arlenko/gem-solder/firmware/source/Core/BSP/Gem/Pins.h

/*
 * Pins.h
 *
 *  Created on: 29 May 2020
 *      Author: Ralim
 */

#ifndef BSP_MINIWARE_PINS_H_
#define BSP_MINIWARE_PINS_H_
#include "configuration.h"

#ifdef MODEL_Gem

#define KEY_A_Pin             GPIO_PIN_9
#define KEY_A_GPIO_Port       GPIOB
#define KEY_B_Pin             GPIO_PIN_8
#define KEY_B_GPIO_Port       GPIOB
#define TMP36_INPUT_Pin       GPIO_PIN_0
#define TMP36_INPUT_GPIO_Port GPIOA
#define TMP36_ADC1_CHANNEL    ADC_CHANNEL_0
#define TMP36_ADC2_CHANNEL    ADC_CHANNEL_0
#define TIP_TEMP_Pin          GPIO_PIN_1
#define TIP_TEMP_GPIO_Port    GPIOA
#define TIP_TEMP_ADC1_CHANNEL ADC_CHANNEL_1
#define TIP_TEMP_ADC2_CHANNEL ADC_CHANNEL_1
#define VIN_Pin               GPIO_PIN_4
#define VIN_GPIO_Port         GPIOA
#define VIN_ADC1_CHANNEL      ADC_CHANNEL_4
#define VIN_ADC2_CHANNEL      ADC_CHANNEL_4
// #define PD_VIN_Pin            GPIO_PIN_6
// #define PD_VIN_GPIO_Port      GPIOA
// #define PD_VIN_ADC1_CHANNEL   ADC_CHANNEL_6
// #define PD_VIN_ADC2_CHANNEL   ADC_CHANNEL_6
// #define OLED_RESET_Pin        GPIO_PIN_7
// #define OLED_RESET_GPIO_Port  GPIOA
#define PWM_Out_Pin           GPIO_PIN_6
#define PWM_Out_GPIO_Port     GPIOA
#define PWM_Out_CHANNEL       TIM_CHANNEL_1
#define TIP_CONTROL_TIMER     TIM3
#define ADC_CONTROL_TIMER     TIM4
#define ADC_CONTROL_TIMER_IRQ TIM4_IRQn
#define ADC_TRIGGER           ADC_EXTERNALTRIGINJECCONV_T4_TRGO
#define SCL_Pin               GPIO_PIN_11
#define SCL_GPIO_Port         GPIOB
#define SDA_Pin               GPIO_PIN_10
#define SDA_GPIO_Port         GPIOB
// PD controller
#define SCL2_Pin       GPIO_PIN_10
#define SCL2_GPIO_Port GPIOA
#define SDA2_Pin       GPIO_PIN_9
#define SDA2_GPIO_Port GPIOA
// #define INT_PD_Pin       GPIO_PIN_7
// #define INT_PD_GPIO_Port GPIOB
// Selecting the DC source to route to theg
// #define DC_SELECT_Pin       GPIO_PIN_4
// #define DC_SELECT_GPIO_Port GPIOB
// #define PD_SELECT_Pin       GPIO_PIN_15
// #define PD_SELECT_GPIO_Port GPIOA

// #define TIP_RESISTANCE_SENSE_Pin       GPIO_PIN_1
// #define TIP_RESISTANCE_SENSE_GPIO_Port GPIOA

#define STAND_SENSE_Pin          GPIO_PIN_5
#define STAND_SENSE_GPIO_Port    GPIOA
#define STAND_SENSE_ADC2_CHANNEL ADC_CHANNEL_5

#define CURRENT_SENSE_Pin          GPIO_PIN_2
#define CURRENT_SENSE_GPIO_Port    GPIOA
#define CURRENT_SENSE_ADC1_CHANNEL ADC_CHANNEL_2
#define CURRENT_SENSE_ADC2_CHANNEL ADC_CHANNEL_2

#define WS2812_Pin       GPIO_PIN_13
#define WS2812_GPIO_Port GPIOB
#endif

#endif /* BSP_MINIWARE_PINS_H_ */
